DUcepticons/Intelligent-Saline/Autocad Compatible/Autocad Images/PCB/PCB_bottomLayer.png

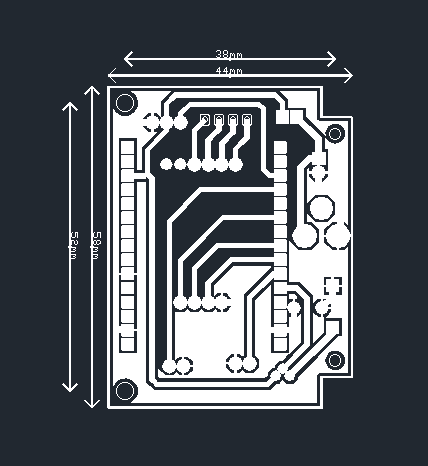
Autocad Compatible/Autocad Images/PCB/PCB_bottomLayer.png
