DUcepticons/Intelligent-Saline/Autocad Compatible/Autocad Images/PCB/PCB_topLayer.png

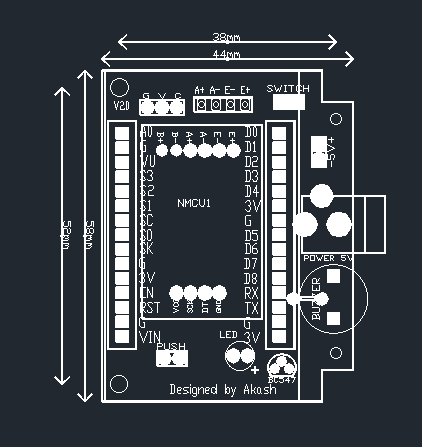
Autocad Compatible/Autocad Images/PCB/PCB_topLayer.png
