DUcepticons/Intelligent-Saline/Autocad Compatible/Autocad Images/Product/Device Only/2D wireframe.png

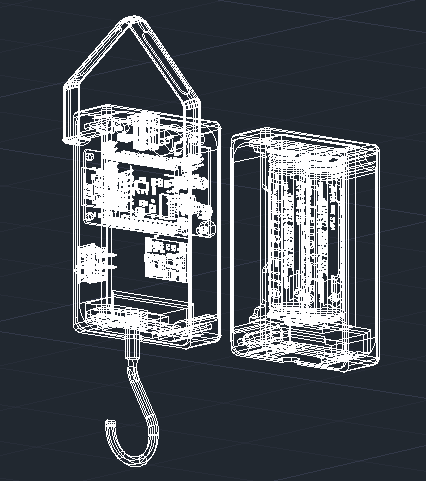
Autocad Compatible/Autocad Images/Product/Device Only/2D wireframe.png
