DUcepticons/Intelligent-Saline/Autocad Compatible/Autocad Images/Product/Device Only/Hidden.png

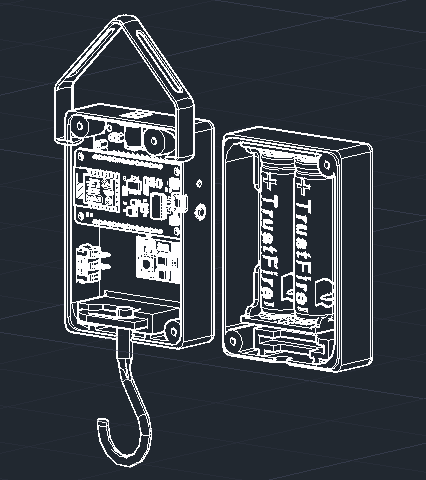
Autocad Compatible/Autocad Images/Product/Device Only/Hidden.png
