DUcepticons/Intelligent-Saline/Autocad Compatible/Autocad Images/Product/Device Only/Realistic.png

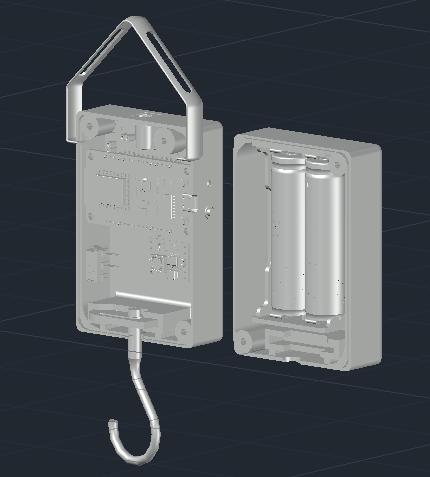
Autocad Compatible/Autocad Images/Product/Device Only/Realistic.png
