DUcepticons/Intelligent-Saline/Autocad Compatible/Autocad Images/Product/Device Only/Shades of gray.png

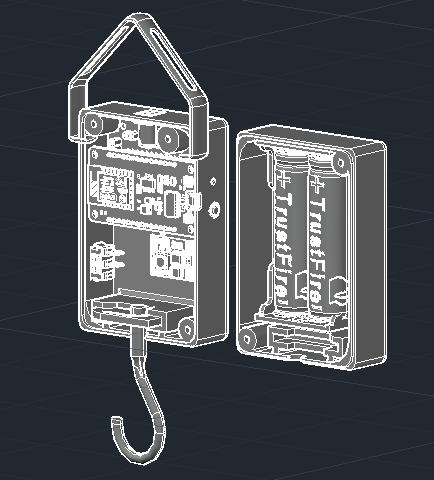
Autocad Compatible/Autocad Images/Product/Device Only/Shades of gray.png
