DUcepticons/Intelligent-Saline/Autocad Compatible/Autocad Images/Product/Flow Controller/Realistic.png

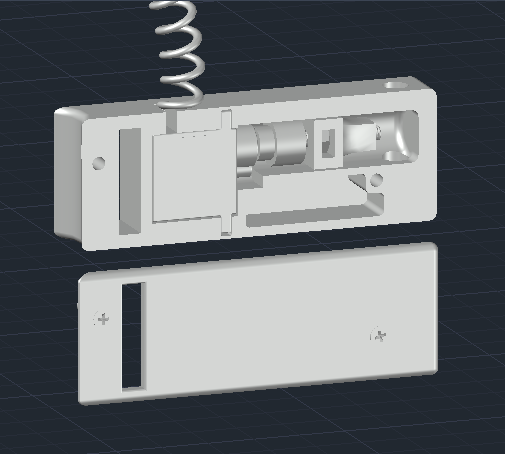
Autocad Compatible/Autocad Images/Product/Flow Controller/Realistic.png
