DUcepticons/Intelligent-Saline/Autocad Compatible/Autocad Images/Product/Flow Controller/Shades of gray.png

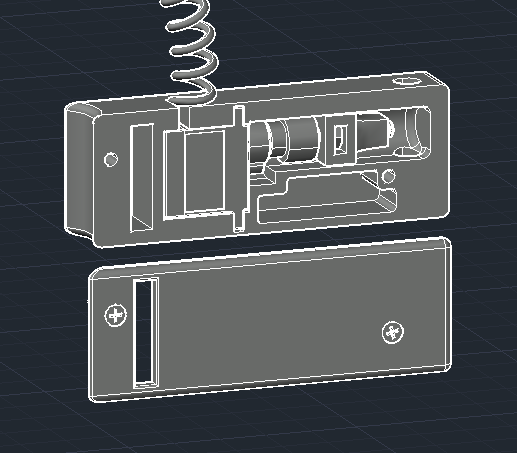
Autocad Compatible/Autocad Images/Product/Flow Controller/Shades of gray.png
