DUcepticons/Intelligent-Saline/Autocad Compatible/Autocad Images/Product/Flow Controller/Wireframe.png

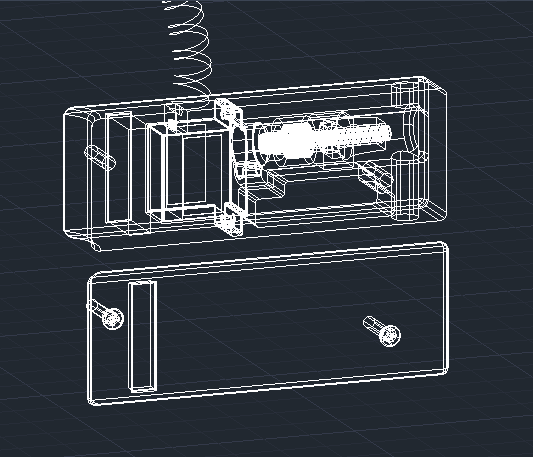
Autocad Compatible/Autocad Images/Product/Flow Controller/Wireframe.png
