DUcepticons/Intelligent-Saline/Autocad Compatible/Autocad Images/Product/Full/Realistic.png

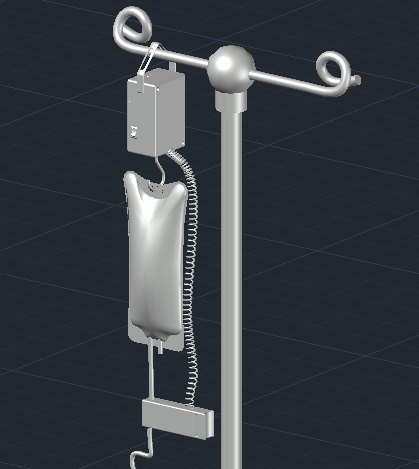
Autocad Compatible/Autocad Images/Product/Full/Realistic.png
