DUcepticons/Intelligent-Saline/Autocad Compatible/Autocad Images/Product/Full/Shaded.png

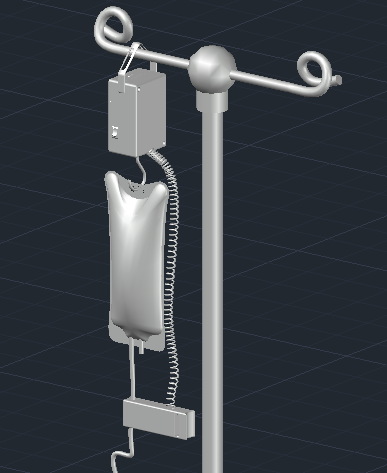
Autocad Compatible/Autocad Images/Product/Full/Shaded.png
