DUcepticons/Intelligent-Saline/Autocad Compatible/Autocad Images/Product/Full/Wareframe.png

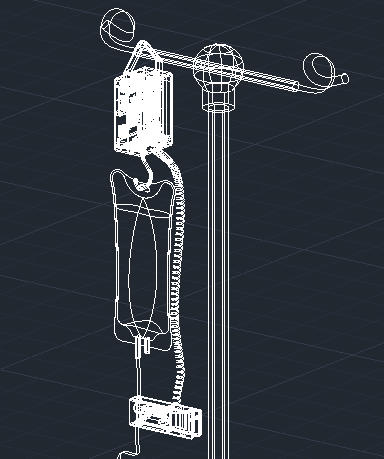
Autocad Compatible/Autocad Images/Product/Full/Wareframe.png
