DUcepticons/Intelligent-Saline/Autocad Compatible/Product Design/To view 3D model.png

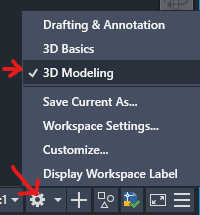
Autocad Compatible/Product Design/To view 3D model.png
