DUcepticons/Intelligent-Saline/Device Images/1.png

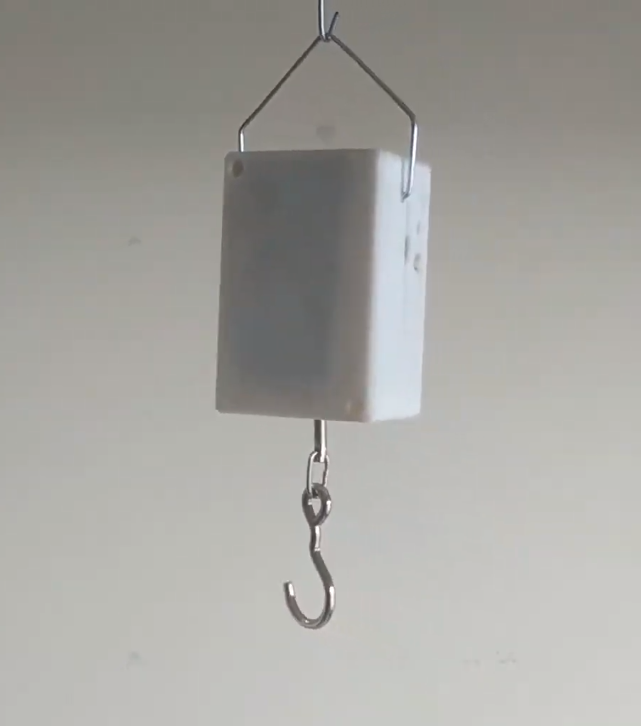
Device Images/1.png
