DUcepticons/Intelligent-Saline/Device Images/123.png

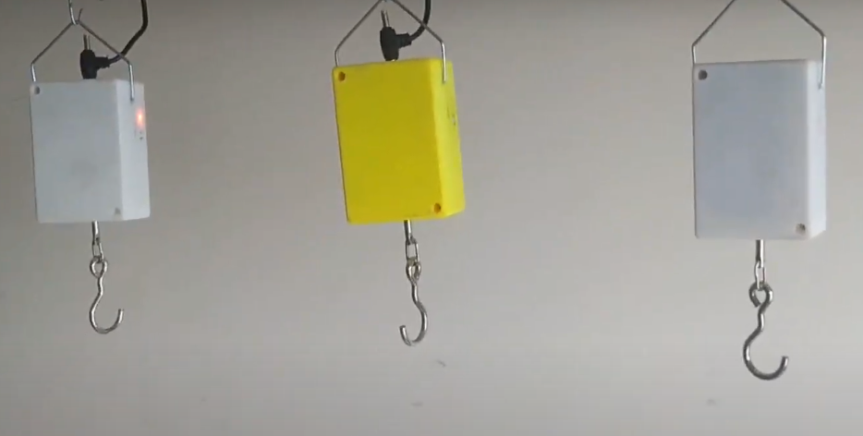
Device Images/123.png
