DUcepticons/Intelligent-Saline/Device Images/123_1.jpg

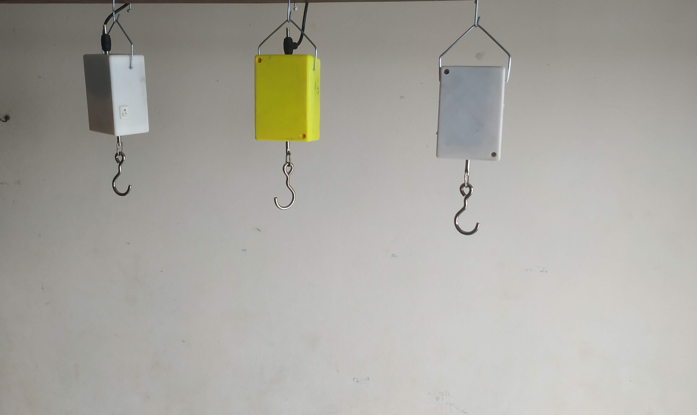
Device Images/123_1.jpg
