DUcepticons/Intelligent-Saline/Device Images/123_loaded.jpg

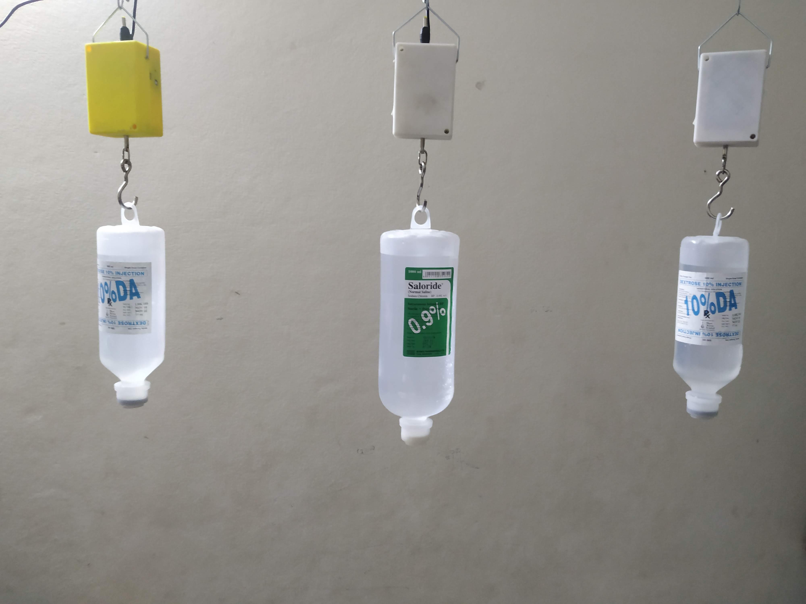
Device Images/123_loaded.jpg
