DUcepticons/Intelligent-Saline/Device Images/Final version.jpg

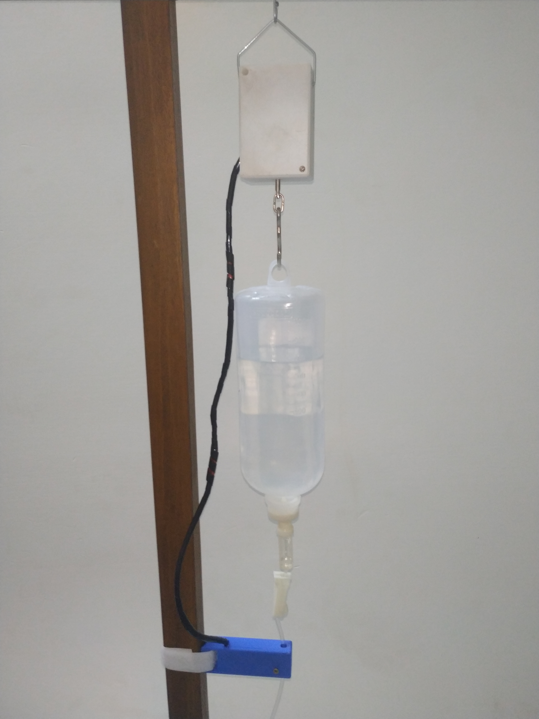
Device Images/Final version.jpg
