DUcepticons/Intelligent-Saline/Device Images/Flow blocker_rendered.jpg

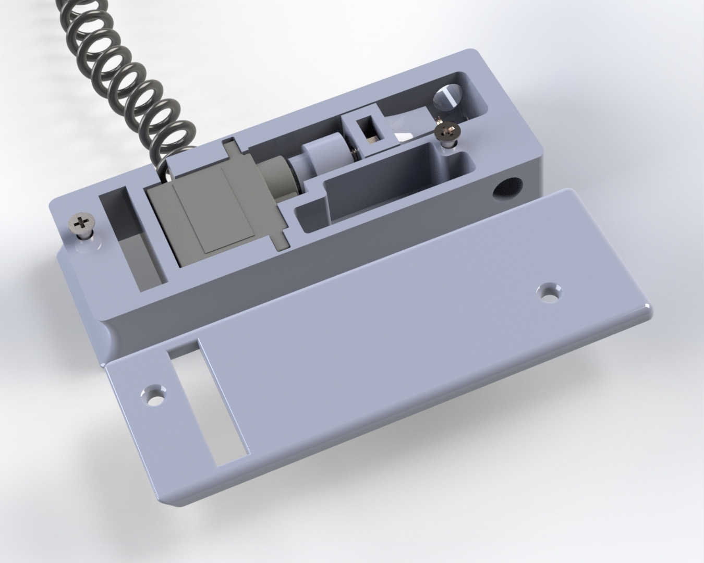
Device Images/Flow blocker_rendered.jpg
