DUcepticons/Intelligent-Saline/Device Images/Front view.jpg

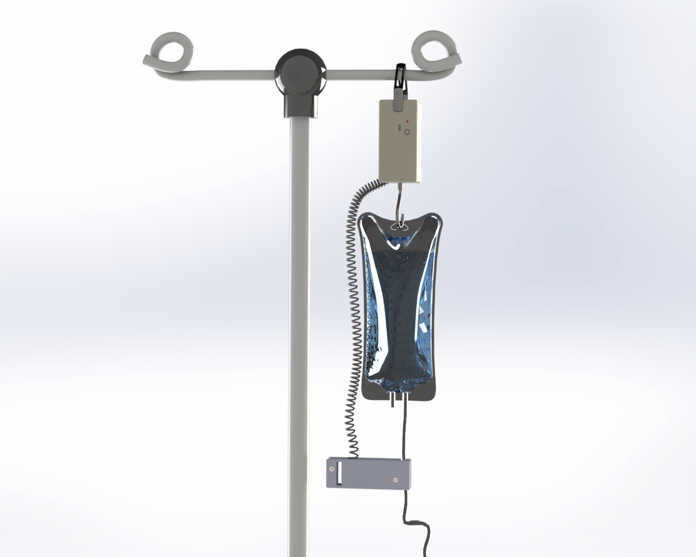
Device Images/Front view.jpg
