DUcepticons/Intelligent-Saline/Device Images/full view.jpg

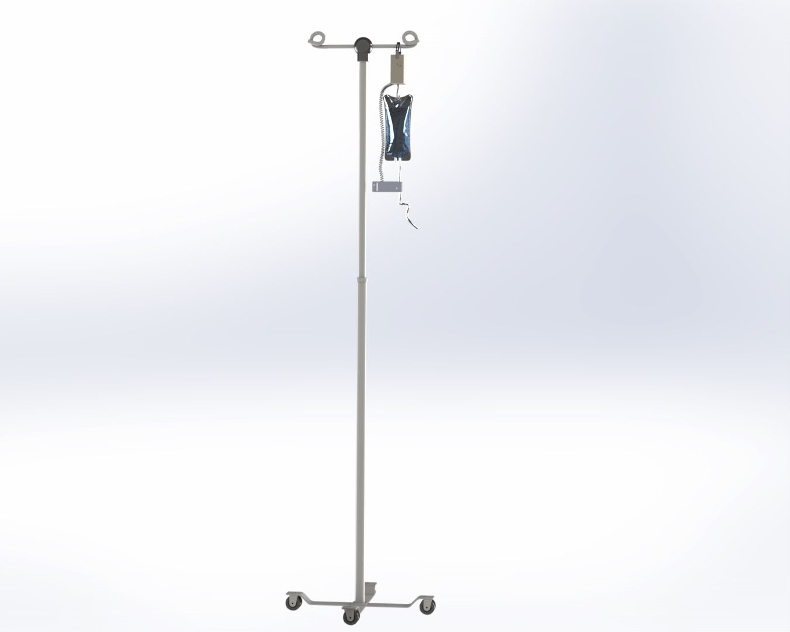
Device Images/full view.jpg
