DUcepticons/Intelligent-Saline/Device Images/Inside2.jpg

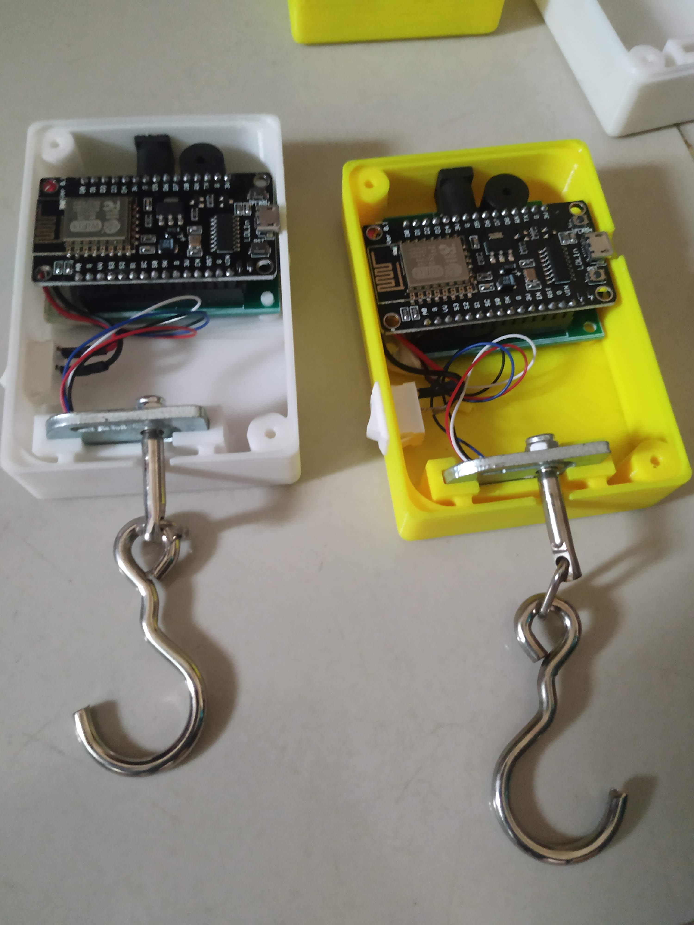
Device Images/Inside2.jpg
