DUcepticons/Intelligent-Saline/Device Images/Inside.png

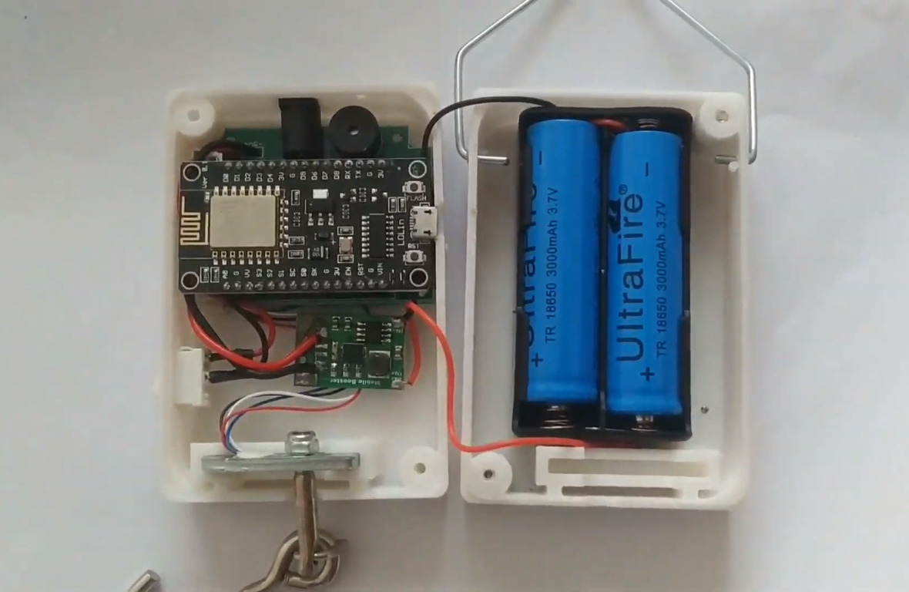
Device Images/Inside.png
