DUcepticons/Intelligent-Saline/Device Images/Mobile photos/IMG_20200905_001722.jpg

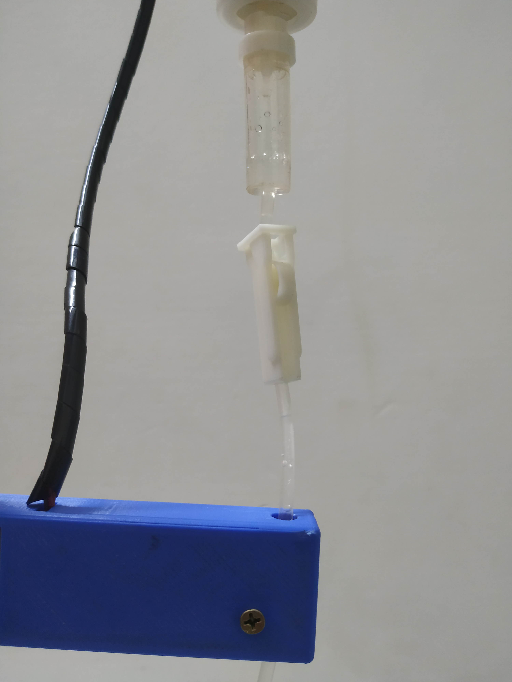
Device Images/Mobile photos/IMG_20200905_001722.jpg
