DUcepticons/Intelligent-Saline/Device Images/Mobile photos/IMG_20200905_170722.jpg

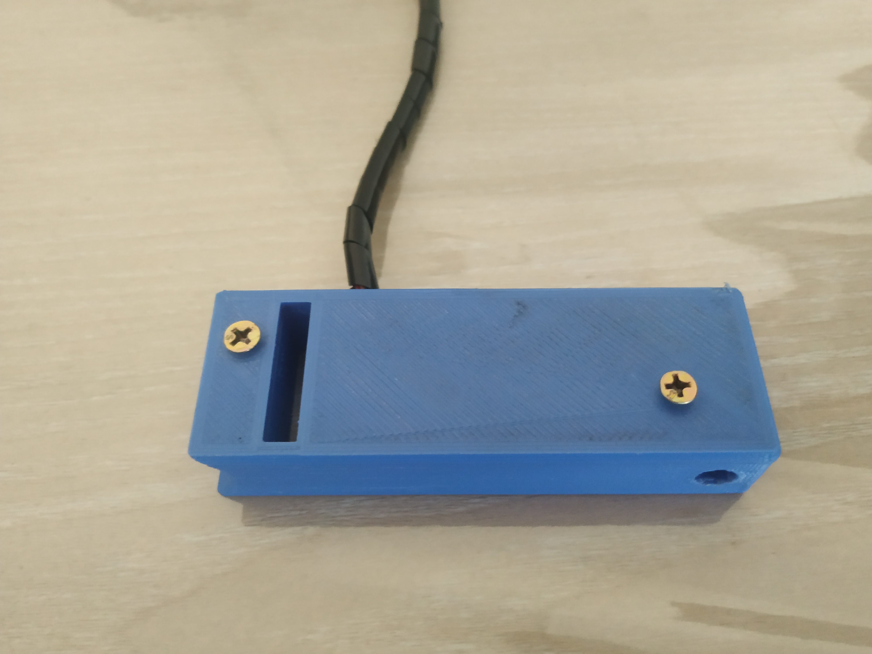
Device Images/Mobile photos/IMG_20200905_170722.jpg
