DUcepticons/Intelligent-Saline/Device Images/Mobile photos/IMG_20200905_171649.jpg

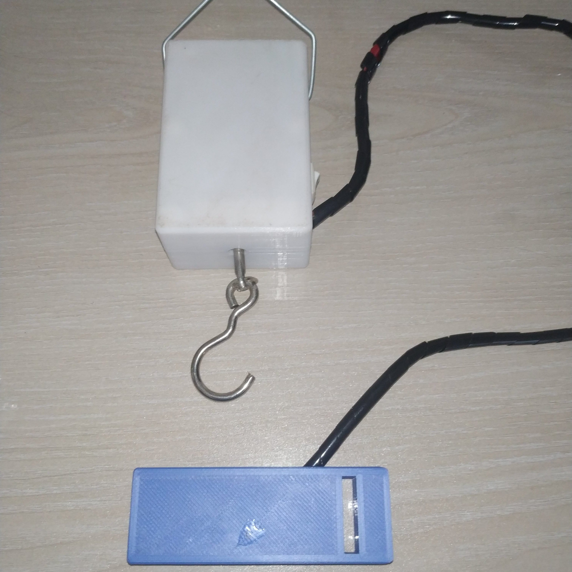
Device Images/Mobile photos/IMG_20200905_171649.jpg
