DUcepticons/Intelligent-Saline/Device Images/Mobile photos/IMG_20200905_171654.jpg

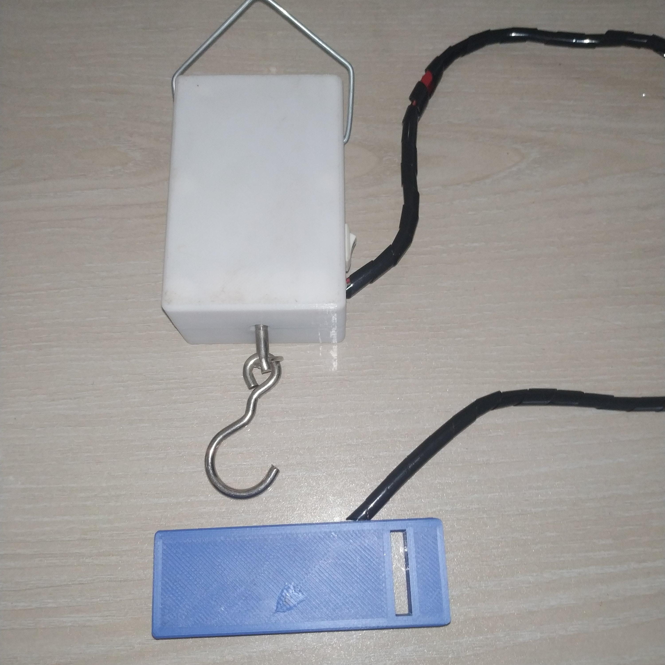
Device Images/Mobile photos/IMG_20200905_171654.jpg
