DUcepticons/Intelligent-Saline/Device Images/Mobile photos/IMG_20200905_171703.jpg

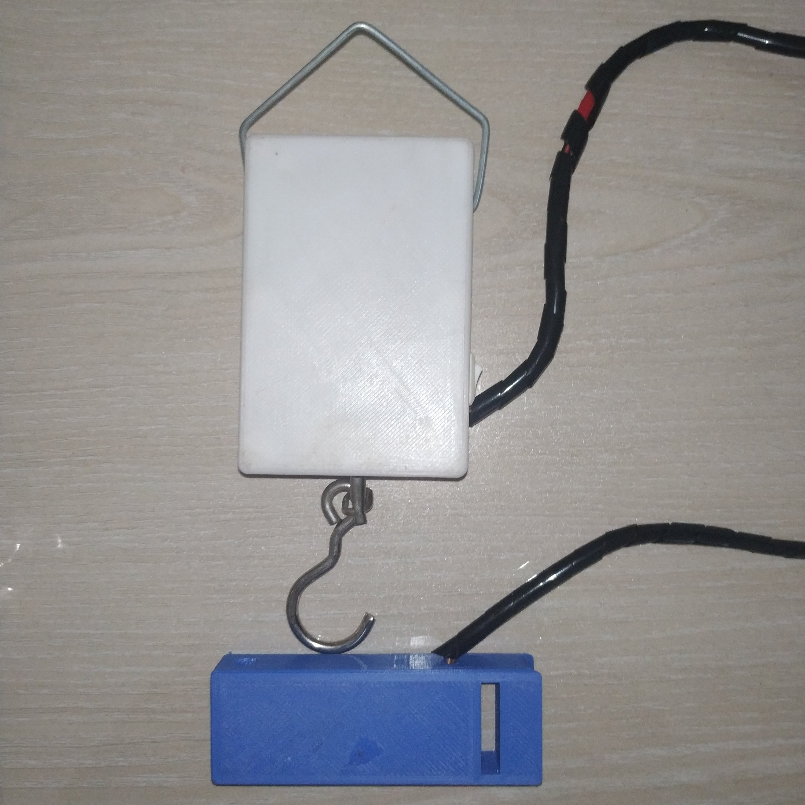
Device Images/Mobile photos/IMG_20200905_171703.jpg
