DUcepticons/Intelligent-Saline/Device Images/Mobile photos/IMG_20200905_171758.jpg

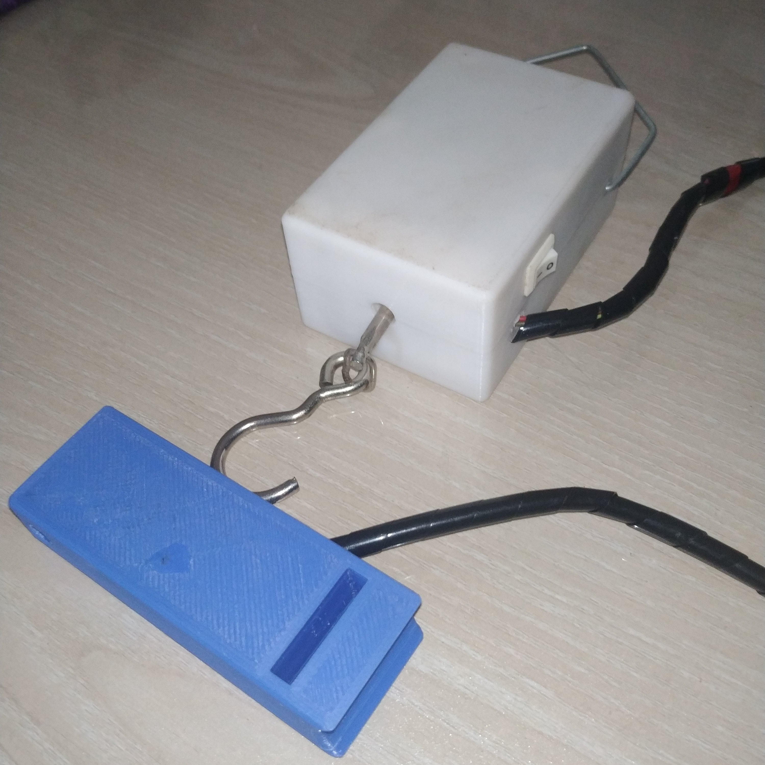
Device Images/Mobile photos/IMG_20200905_171758.jpg
