DUcepticons/Intelligent-Saline/Device Images/Mobile photos/IMG_20200905_172005.jpg

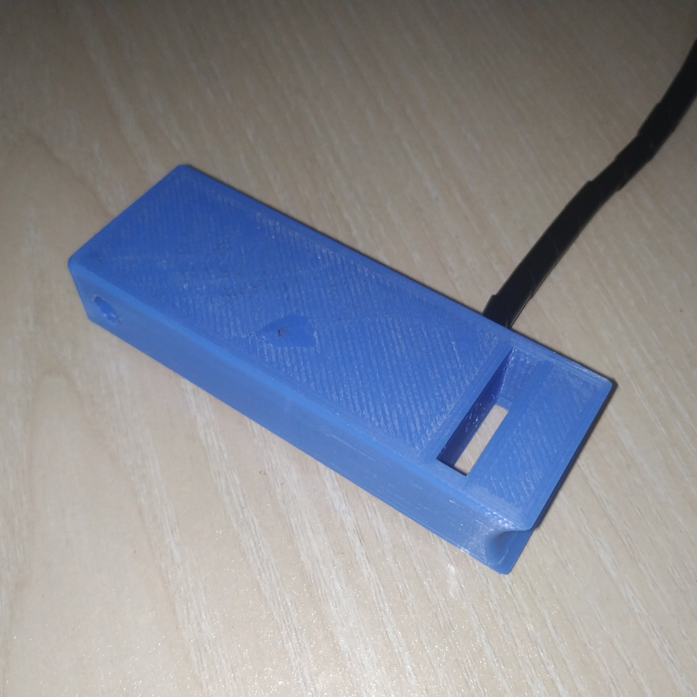
Device Images/Mobile photos/IMG_20200905_172005.jpg
