DUcepticons/Intelligent-Saline/Device Images/Mobile photos/IMG_20200905_172008.jpg

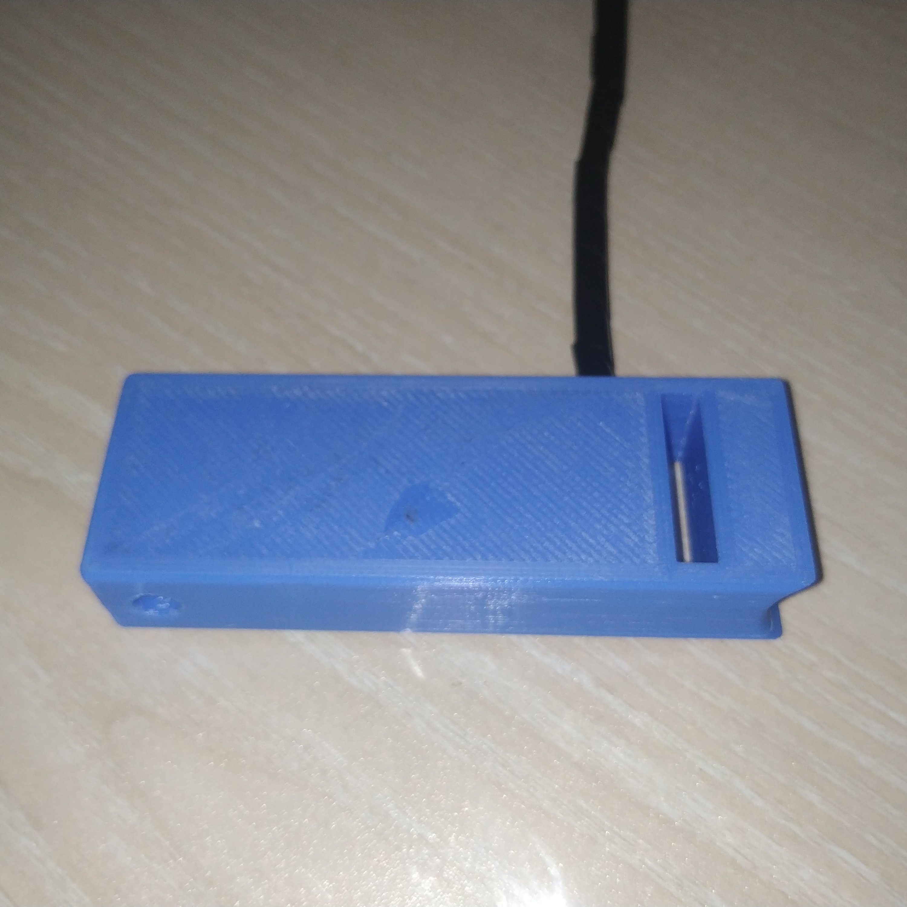
Device Images/Mobile photos/IMG_20200905_172008.jpg
