DUcepticons/Intelligent-Saline/Device Images/Mobile photos/IMG_20200905_172524.jpg

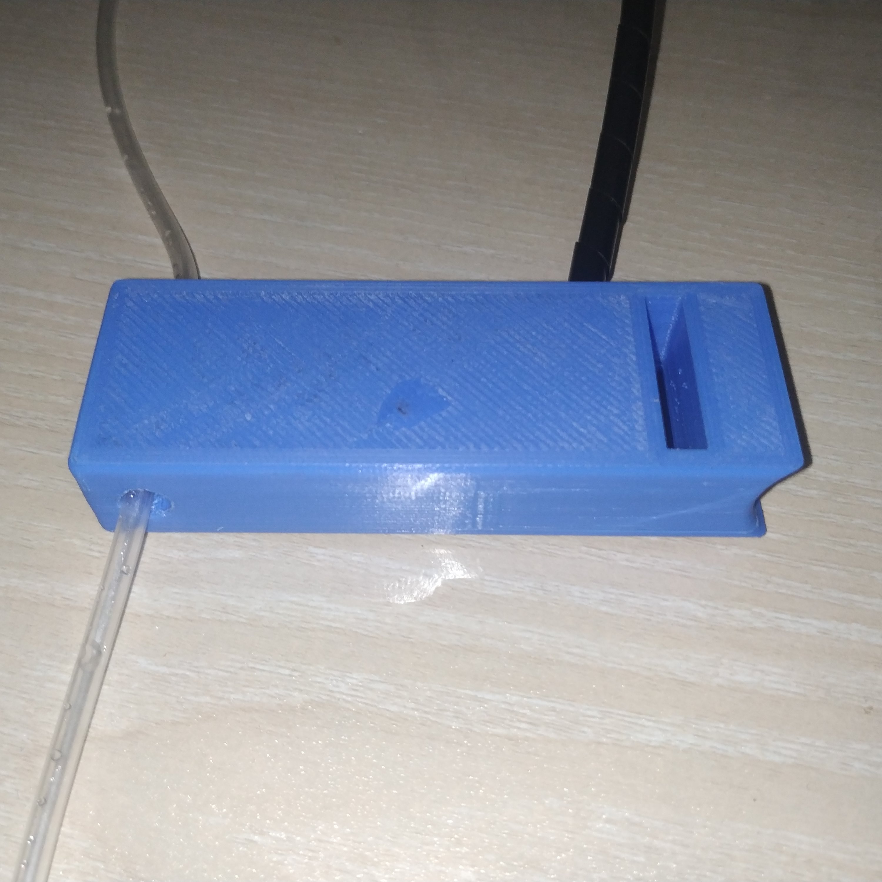
Device Images/Mobile photos/IMG_20200905_172524.jpg
