DUcepticons/Intelligent-Saline/Device Images/Mobile photos/IMG_20200905_172531.jpg

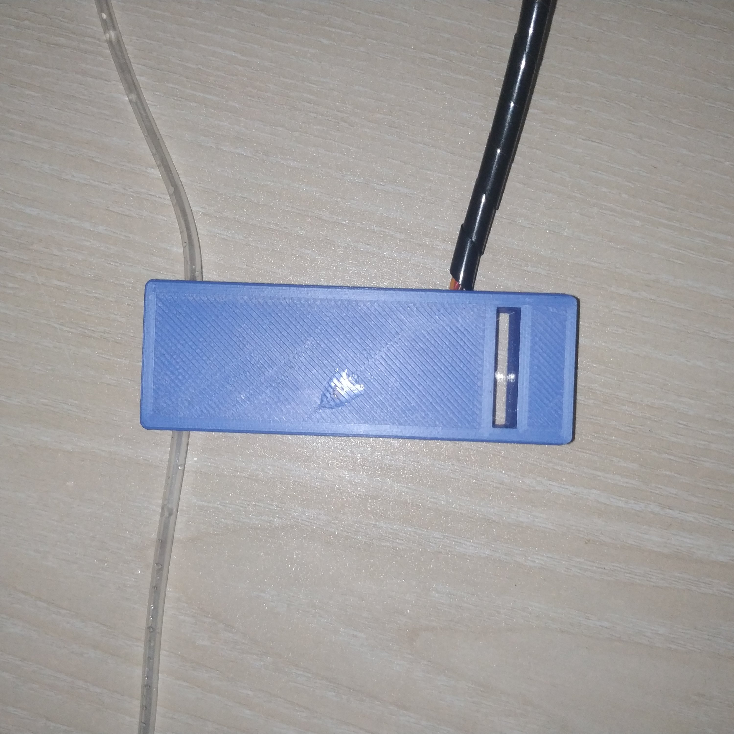
Device Images/Mobile photos/IMG_20200905_172531.jpg
