DUcepticons/Intelligent-Saline/Device Images/Mobile photos/IMG_20200905_172552.jpg

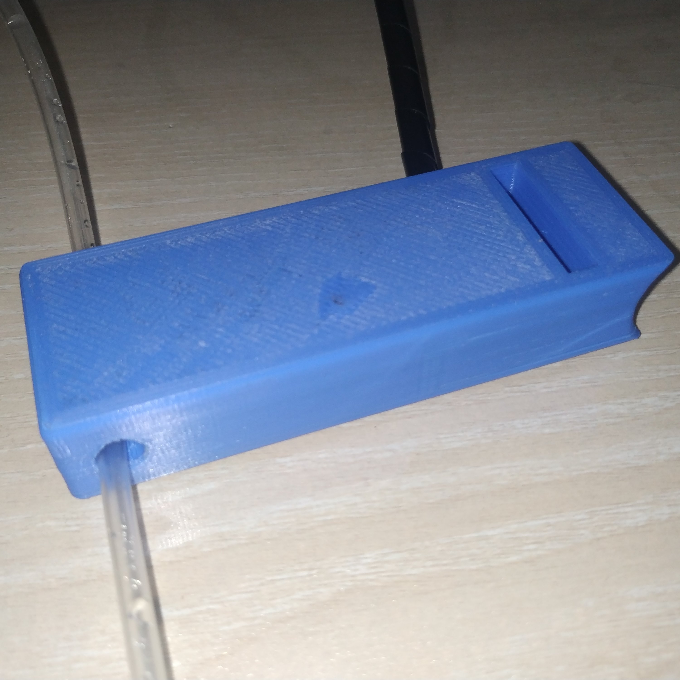
Device Images/Mobile photos/IMG_20200905_172552.jpg
