DUcepticons/Intelligent-Saline/Device Images/Render1.jpg

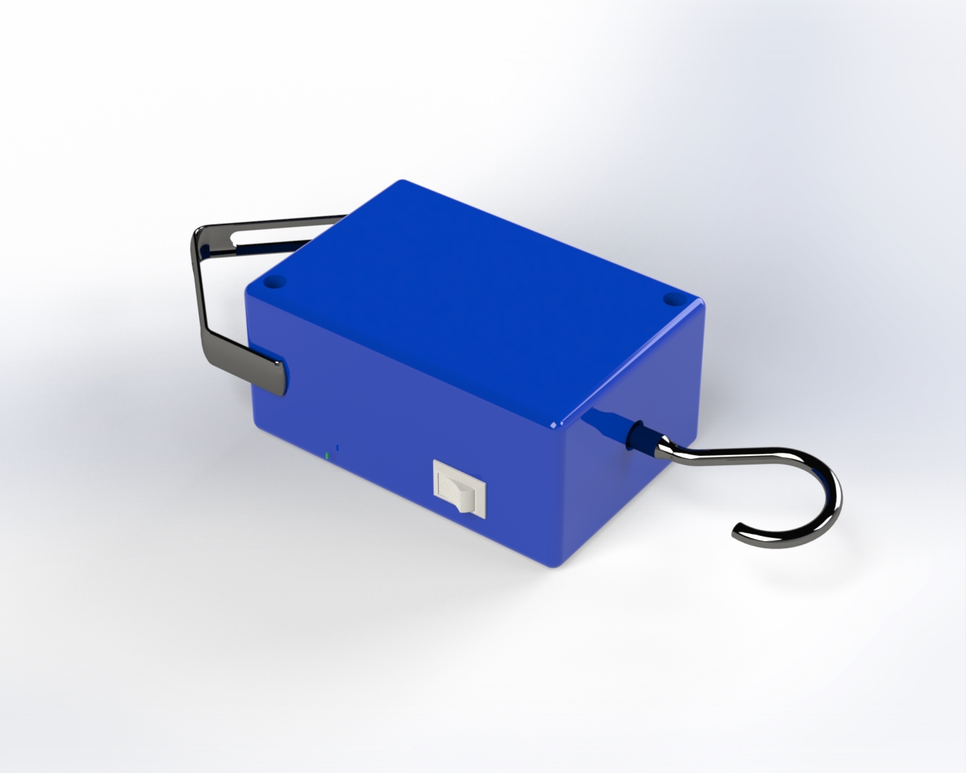
Device Images/Render1.jpg
