DUcepticons/Intelligent-Saline/Device Images/Render2.jpg

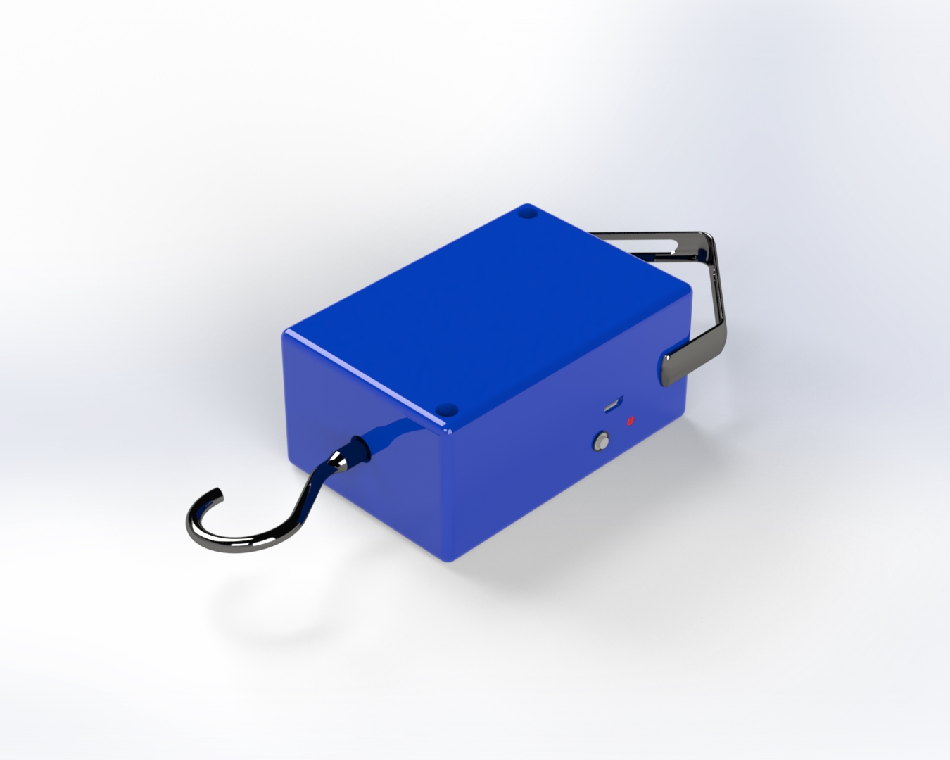
Device Images/Render2.jpg
