DUcepticons/Intelligent-Saline/Device Images/Render3.jpg

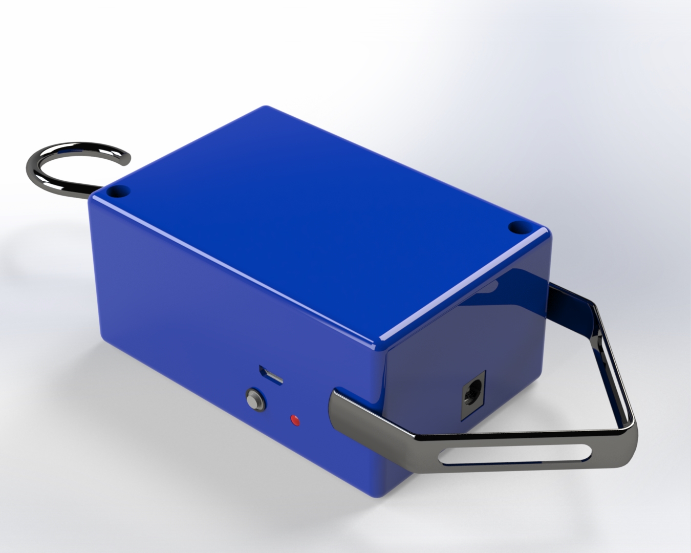
Device Images/Render3.jpg
