DUcepticons/Intelligent-Saline/Device Images/Render4.jpg

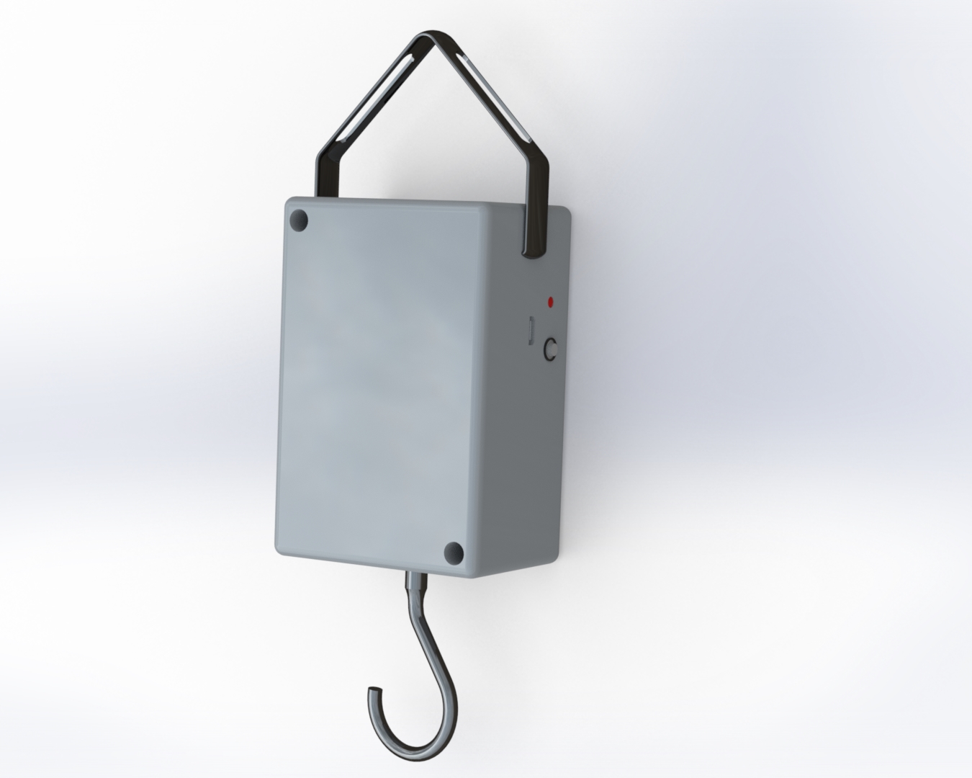
Device Images/Render4.jpg
