DUcepticons/Intelligent-Saline/workflow.png

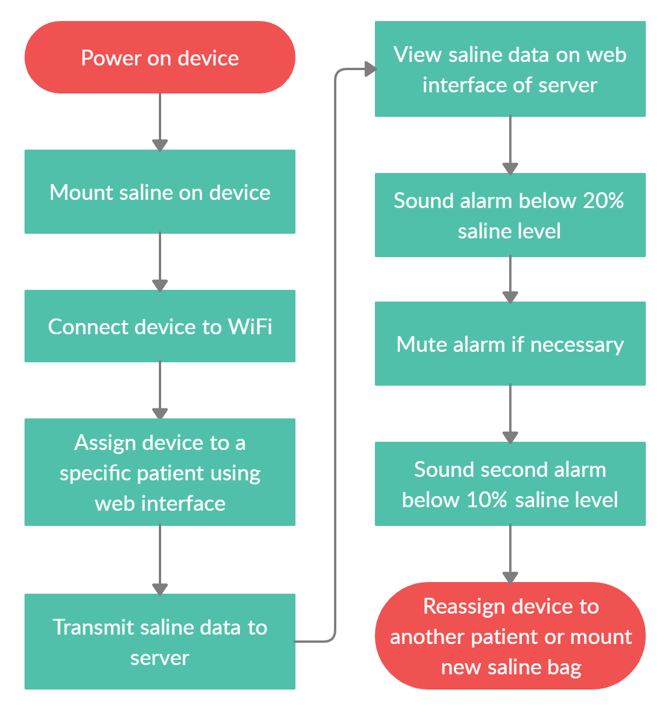
workflow.png
