DUcepticons/Intelligent-Saline/Product Design/V2/flow blocker/Version1 Flow blocker/Servo-MG90S.SLDPRT

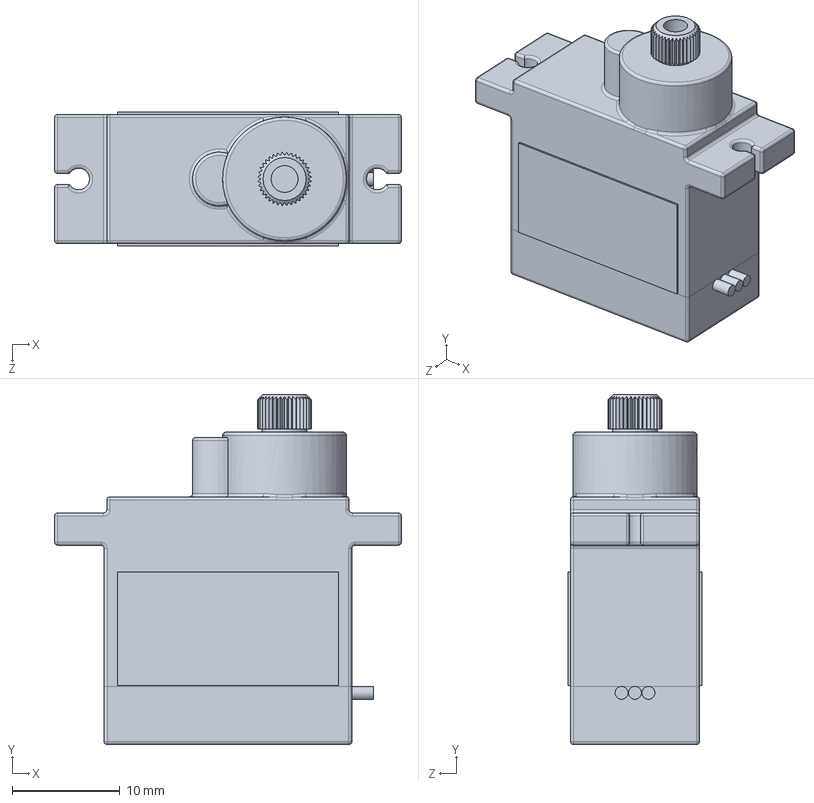
[picture p72: CAD file, 2020-08-02]
Product Design/V2/flow blocker/Version1 Flow blocker/Servo-MG90S.SLDPRT
32.2 x 32.5 x 12.4 mm
