DUcepticons/Intelligent-Saline/Product Design/V2/PushButtonSwitch2Pin.SLDPRT

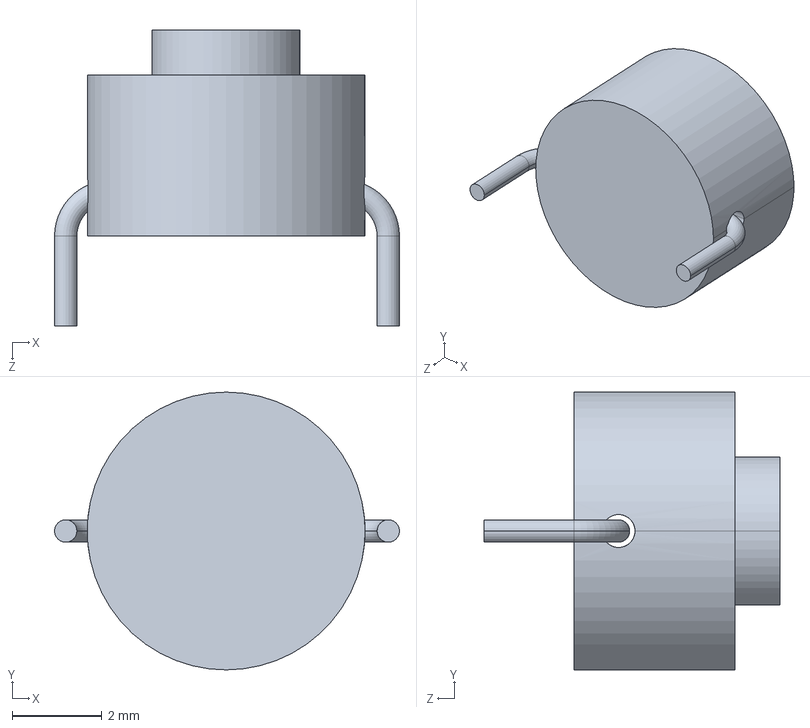
[picture p73: CAD file, 2020-05-31]
Product Design/V2/PushButtonSwitch2Pin.SLDPRT
7.70 x 6.20 x 6.60 mm
