DUcepticons/Intelligent-Saline/Product Design/V2/LED 3mm (Red).SLDPRT

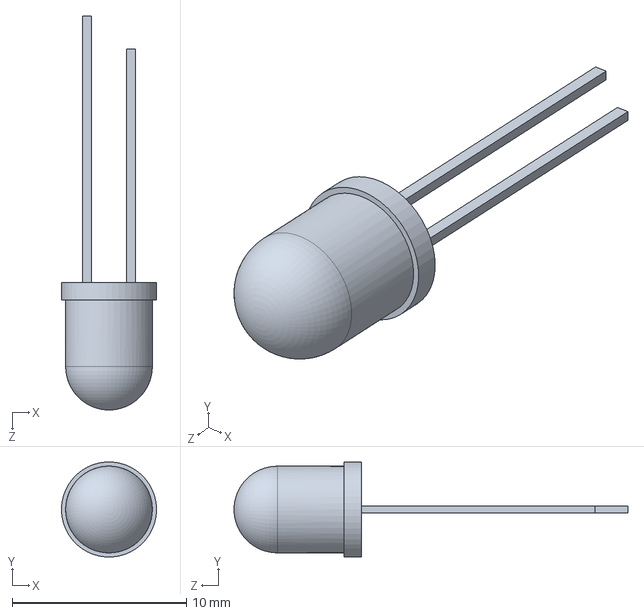
[picture p74: CAD file, 2020-05-31]
Product Design/V2/LED 3mm (Red).SLDPRT
5.46 x 5.45 x 22.6 mm
