DUcepticons/Intelligent-Saline/Product Design/V2/lower_body.SLDPRT

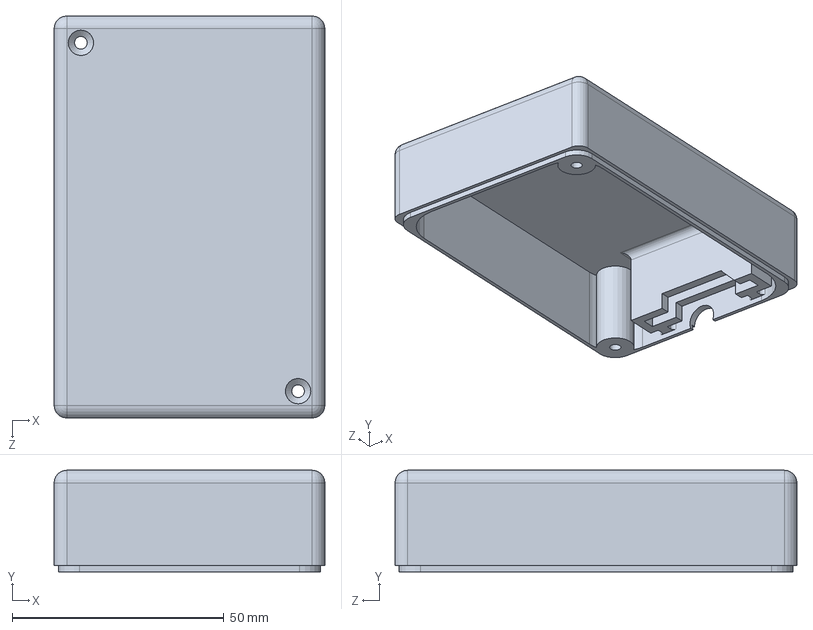
[picture p75: CAD file, 2020-05-31]
Product Design/V2/lower_body.SLDPRT
64.0 x 24.0 x 95.0 mm
