DUcepticons/Intelligent-Saline/Product Design/V2/Hanger.SLDPRT

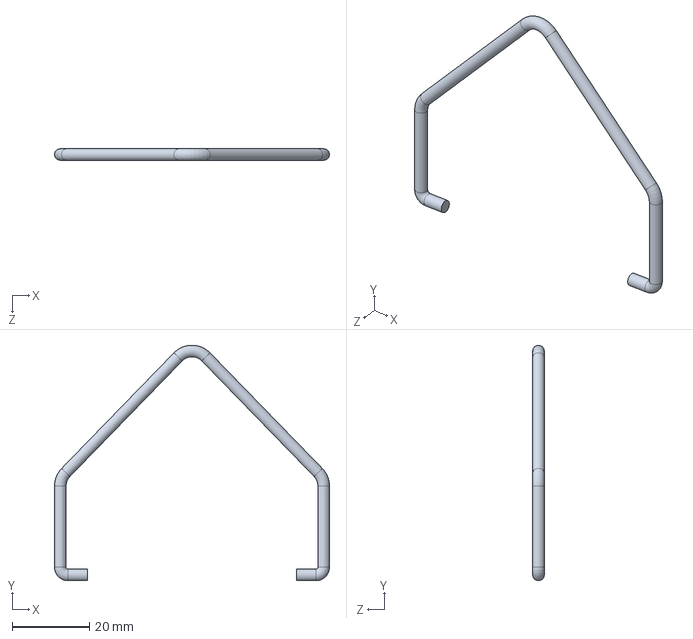
[picture p76: CAD file, 2020-05-31]
Product Design/V2/Hanger.SLDPRT
71.0 x 60.8 x 3.00 mm
