DUcepticons/Intelligent-Saline/Product Design/V2/Hanger 2.SLDPRT

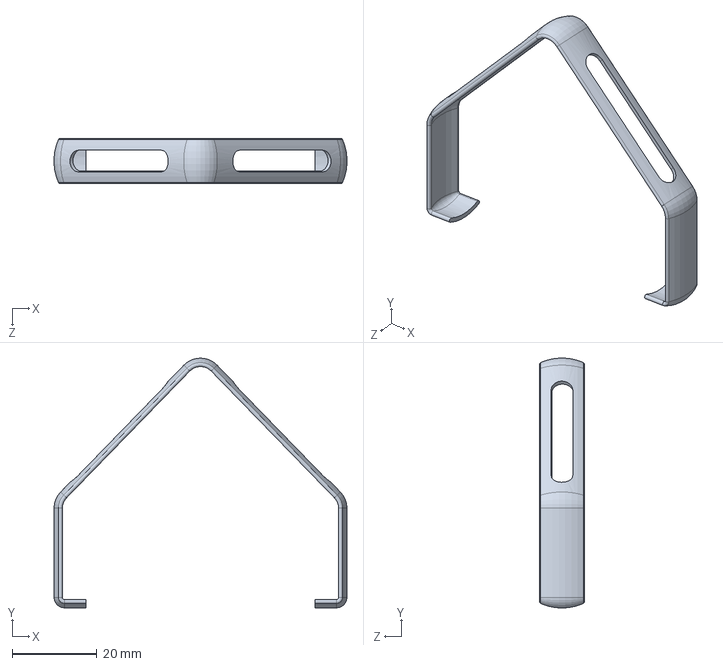
[picture p77: CAD file, 2020-05-31]
Product Design/V2/Hanger 2.SLDPRT
69.0 x 58.8 x 10.6 mm
