DUcepticons/Intelligent-Saline/Product Design/V2/2-Pin ON-OFF Switch.SLDPRT

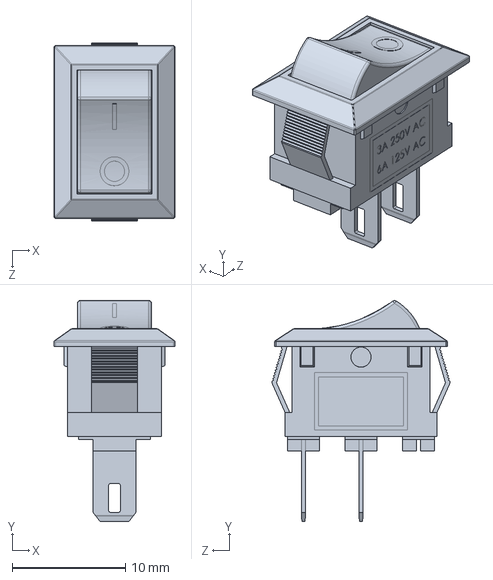
[picture p78: CAD file, 2020-01-11]
Product Design/V2/2-Pin ON-OFF Switch.SLDPRT
10.7 x 19.5 x 15.7 mm
