DUcepticons/Intelligent-Saline/Product Design/V2/batt-case-18650.SLDPRT

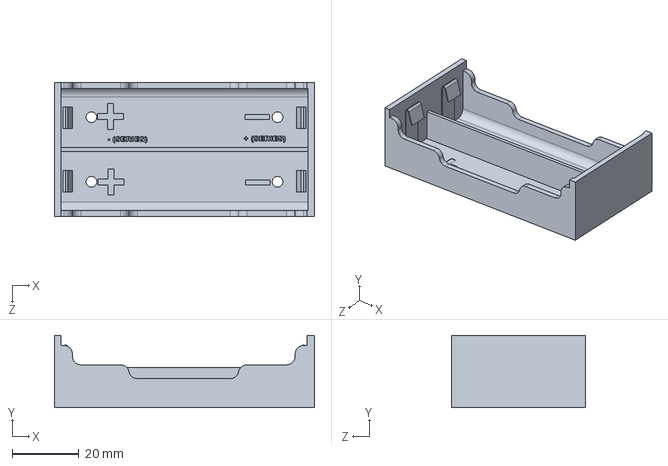
[picture p79: CAD file, 2020-01-11]
Product Design/V2/batt-case-18650.SLDPRT
77.7 x 21.6 x 40.1 mm
